johnjsb/DAPrototype/src/image_processor.cpp

/******************************************************************************************
  Date:    12.08.2016
  Author:  Nathan Greco (Nathan.Greco@gmail.com)

  Project:
      DAPrototype: Driver Assist Prototype
	  http://github.com/NateGreco/DAPrototype.git

  License:
	  This software is licensed under GNU GPL v3.0
	  
******************************************************************************************/

//Standard libraries
#include <iostream>
#include <algorithm> 
#include <mutex>
#include <atomic>
#include <deque>
#include <array>
#include <exception>
#include <string>

//3rd party libraries
#include "opencv2/opencv.hpp"

//Project libraries
#include "lane_detect_processor.h"
#include "pace_setter_class.h"
#include "process_values_class.h"
#include "xml_reader.h"

/*****************************************************************************************/
void ProcessImageThread( cv::Mat *orgimage,
                         std::mutex *capturemutex,
						 ProcessValues *processvalues,
                         std::atomic<bool> *exitsignal )
{

	std::cout << "Image processor thread starting!" << '\n';
	
	//Check if LDW is enabled
	if ( !settings::ldw::kenabled ) {
		std::cout << "LDW disabled, exiting image processor thread!" << '\n';
		return;
	}
	
	//create pace setter
	PaceSetter processorpacer(settings::ldw::kupdatefps, "image processor");
	
	//Check image is initialized
	while ( orgimage->empty() ) {
		if (*exitsignal) {
			return;
		}
		processorpacer.SetPace();		
	}

	//Create thread variables
	std::deque<Polygon> pastpolygons;

	//Loop indefinitely
	while( !(*exitsignal) ) {
		try {
			if ( (processvalues->gpsstatus_ != 2) && settings::ldw::kenabled ) {
				//Get image
				capturemutex->lock();
				cv::Mat processimage{ *orgimage };
				capturemutex->unlock();
				
				//Get lanes
				Polygon newpolygon;
				ProcessImage( processimage, newpolygon );
				AveragePolygon( newpolygon,
								pastpolygons,
								settings::ldw::ksamplestoaverage,
								settings::ldw::ksamplestokeep );	

				//Evaluate LDW
				if ( newpolygon[0] != cv::Point(0,0) ) {
					double deviationpix = 0.5 * ( newpolygon[0].x + 
												  newpolygon[1].x - 
												  settings::cam::kpixwidth );
					double deviationper = 100.0 * deviationpix /
										  static_cast<double>(newpolygon[1].x -
															  newpolygon[0].x);	
					if ( settings::ldw::kperoffsetalarm < deviationper ) {
						processvalues->ldwstatus_ = LDW_LEFT_DEVIATION_ALARM;
					} else if ( (settings::ldw::kperoffsetwarning < deviationper) &&
								(deviationper < settings::ldw::kperoffsetalarm) ) {
						processvalues->ldwstatus_ = LDW_LEFT_DEVIATION_WARNING;
					} else if ( (0.0 < deviationper) &&
								(deviationper < settings::ldw::kperoffsetwarning) ) {
						processvalues->ldwstatus_ = LDW_LEFT_DEVIATION_OK;
					} else if ( (0.0 > deviationper) &&
								(deviationper > -settings::ldw::kperoffsetwarning) ) {
						processvalues->ldwstatus_ = LDW_RIGHT_DEVIATION_OK;
					} else if ( (-settings::ldw::kperoffsetwarning > deviationper) &&
								(deviationper > -settings::ldw::kperoffsetalarm) ) {
						processvalues->ldwstatus_ = LDW_RIGHT_DEVIATION_WARNING;
					} else if ( -settings::ldw::kperoffsetalarm > deviationper ) {
						processvalues->ldwstatus_ = LDW_RIGHT_DEVIATION_ALARM;
					}
				} else {
					processvalues->ldwstatus_ = LDW_ERROR;
				}
				//Write new data
				processvalues->SetPolygon(newpolygon);
			} else {
				processvalues->ldwstatus_ = LDW_INACTIVE;
			}
			
			processorpacer.SetPace();
		} catch ( const std::exception& ex ) {
			std::cout << "Image Processor thread threw exception: "<< ex.what() << '\n';
		} catch ( const std::string& str ) {
			std::cout << "Image Processor thread threw exception: "<< str << '\n';
		} catch (...) {
			std::cout << "Image Processor thread threw exception of unknown type!" << '\n';
		}
	}
	
	std::cout << "Exiting image processor thread!" << '\n';
	return;
}
